matthiasklein/Pikado/photos/interface_v2_prototype.jpg

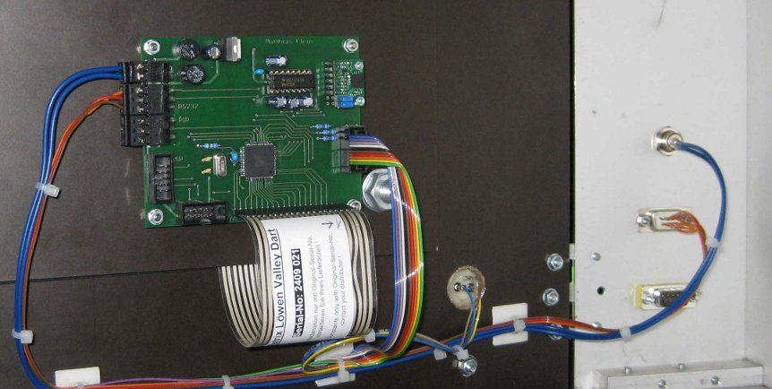
photos/interface_v2_prototype.jpg
